AxLab-UofC/Threading-Space/general_planner_v1.0.1/images/0.png

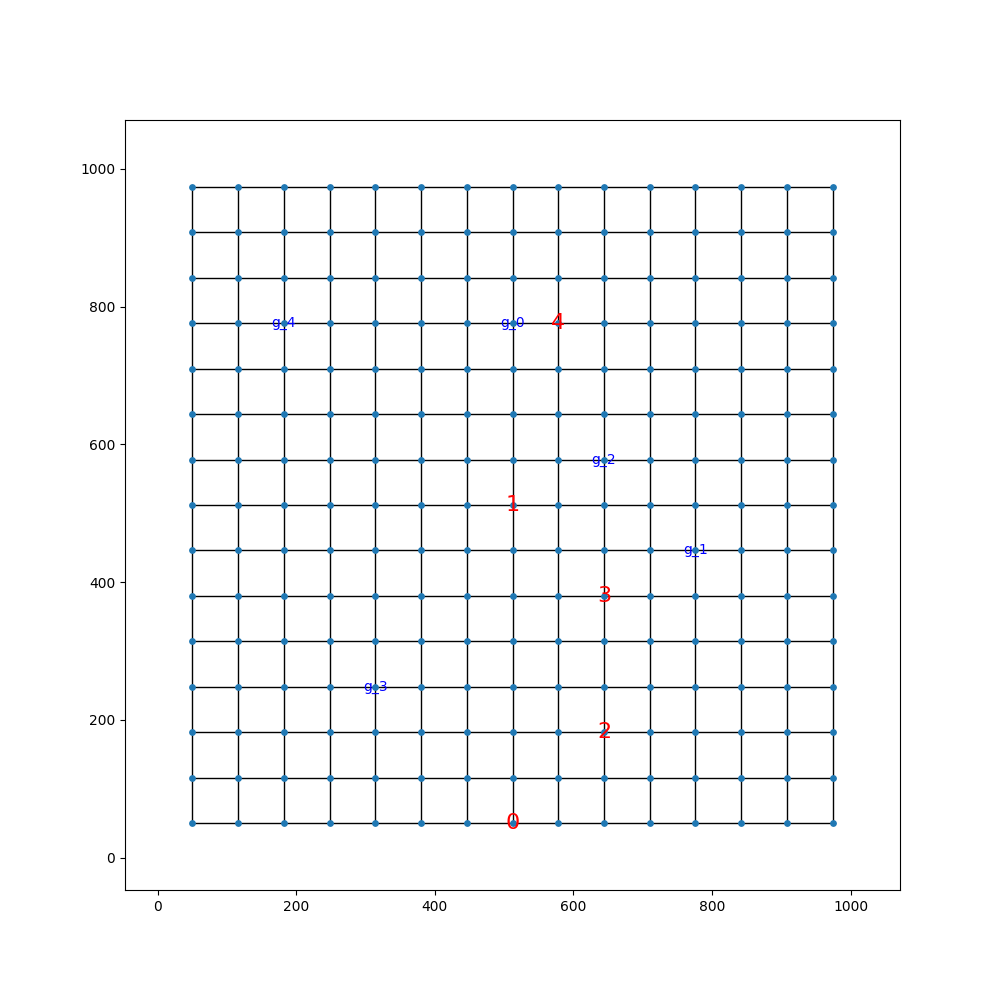
general_planner_v1.0.1/images/0.png
