AxLab-UofC/Threading-Space/Threading_Space/oscSend.pde

//basic motor control (simplified), specification found at:
//can use negative numbers to move toio backwards
//https://toio.github.io/toio-spec/en/docs/ble_motor#motor-control
void motorBasic(int cubeId, int leftspeed, int rightspeed) {
  int hostId = cubeId/cubesPerHost;
  int actualcubeid = cubeId % cubesPerHost;
  OscMessage msg = new OscMessage("/motorbasic");
  msg.add(actualcubeid);
  if (leftspeed < 0) {
    msg.add(0x01);
  } else {
    msg.add(0x02);
  }
  msg.add(leftspeed);
    if (rightspeed < 0) {
    msg.add(0x01);
  } else {
    msg.add(0x02);
  }
  msg.add(rightspeed);
  oscP5.send(msg, server[hostId]);
}

//basic motor control (advanced), specification found at:
//https://toio.github.io/toio-spec/en/docs/ble_motor#motor-control
void motorBasic(int cubeId, boolean leftforwards, int leftspeed, boolean rightforwards, int rightspeed) {
  int hostId = cubeId/cubesPerHost;
  int actualcubeid = cubeId % cubesPerHost;

  if (!cubes[actualcubeid].onFloor) {
    int tempspeed = rightspeed;
    rightspeed = leftspeed;
    leftspeed = tempspeed;

    boolean tempforwards = rightforwards;
    rightforwards = leftforwards;
    leftforwards = tempforwards;
  }

  OscMessage msg = new OscMessage("/motorbasic");
  msg.add(actualcubeid);
  if (leftforwards) {
    msg.add(0x01);
  } else {
    msg.add(0x02);
  }
  msg.add(leftspeed);
    if (rightforwards) {
    msg.add(0x01);
  } else {
    msg.add(0x02);
  }
  msg.add(rightspeed);
  oscP5.send(msg, server[hostId]);
}

//basic motor control (simplified), specification found at:
//can use negative numbers to move toio backwards
//https://toio.github.io/toio-spec/en/docs/ble_motor#motor-control
void motorDuration(int cubeId, int speed, int duration) {
  int hostId = cubeId/cubesPerHost;
  int actualcubeid = cubeId % cubesPerHost;
  OscMessage msg = new OscMessage("/motorduration");
  msg.add(actualcubeid);
  if (speed < 0) {
    msg.add(0x01);
  } else {
    msg.add(0x02);
  }
  msg.add(speed);
    if (speed < 0) {
    msg.add(0x01);
  } else {
    msg.add(0x02);
  }
  msg.add(speed);
  msg.add(duration);
  oscP5.send(msg, server[hostId]);
}

//basic motor control (simplified), specification found at:
//can use negative numbers to move toio backwards
//https://toio.github.io/toio-spec/en/docs/ble_motor#motor-control
void motorDuration(int cubeId, int leftspeed, int rightspeed, int duration) {
  int hostId = cubeId/cubesPerHost;
  int actualcubeid = cubeId % cubesPerHost;
  OscMessage msg = new OscMessage("/motorduration");
  msg.add(actualcubeid);
  if (leftspeed < 0) {
    msg.add(0x01);
  } else {
    msg.add(0x02);
  }
  msg.add(leftspeed);
    if (rightspeed < 0) {
    msg.add(0x01);
  } else {
    msg.add(0x02);
  }
  msg.add(rightspeed);
  msg.add(duration);
  
  oscP5.send(msg, server[hostId]);
}

//basic motor control (advanced), specification found at:
//https://toio.github.io/toio-spec/en/docs/ble_motor#motor-control
void motorDuration(int cubeId, boolean leftforwards, int leftspeed, boolean rightforwards, int rightspeed, int duration) {
  int hostId = cubeId/cubesPerHost;
  int actualcubeid = cubeId % cubesPerHost;
  OscMessage msg = new OscMessage("/motorduration");
  msg.add(actualcubeid);
  if (leftforwards) {
    msg.add(0x01);
  } else {
    msg.add(0x02);
  }
  msg.add(leftspeed);
    if (rightforwards) {
    msg.add(0x01);
  } else {
    msg.add(0x02);
  }
  msg.add(rightspeed);
  msg.add(duration);
  oscP5.send(msg, server[hostId]);
}

//motor control with target specified (simplified), specification found at:
//https://toio.github.io/toio-spec/en/docs/ble_motor#motor-control-with-target-specified
//control, timeout, maxspeed, and speed change are preset
void motorTarget(int cubeId, int mode, int x, int y, int theta){
  int hostId = cubeId/cubesPerHost;
  int actualcubeid = cubeId % cubesPerHost;

   if (!cubes[cubeId].onFloor) {
    x = xmax - x + xmin;;
    theta = 360 - theta;
  }

  OscMessage msg = new OscMessage("/motortarget");
  msg.add(actualcubeid);
  msg.add(mode);
  msg.add(x);
  msg.add(y);
  msg.add(theta);
  oscP5.send(msg, server[hostId]);
}

//motor control with target specified (advanced), specification found at:
//https://toio.github.io/toio-spec/en/docs/ble_motor#motor-control-with-target-specified
void motorTarget(int cubeId, int control, int timeout, int mode, int maxspeed, int speedchange,  int x, int y, int theta){
  int hostId = cubeId/cubesPerHost;
  int actualcubeid = cubeId % cubesPerHost;

  if (!cubes[cubeId].onFloor) {
    x = xmax - x + xmin;;
    theta = 360 - theta;
  }

  OscMessage msg = new OscMessage("/motortarget");
  msg.add(actualcubeid);
  msg.add(control);
  msg.add(timeout);
  msg.add(mode);
  msg.add(maxspeed);
  msg.add(speedchange);
  msg.add(x);
  msg.add(y);
  msg.add(theta);
  oscP5.send(msg, server[hostId]);
}

//motor control with multiple targets specified (simplified), specification found at:
//https://toio.github.io/toio-spec/en/docs/ble_motor#motor-control-with-target-specified
//targets should be formatted as {x, y, theta} or {x, y}. Unless specified, theta = 0
void motorMultiTarget(int cubeId, int mode, int[][] targets) {
  int hostId = cubeId/cubesPerHost;
  int actualcubeid = cubeId % cubesPerHost;
  OscMessage msg = new OscMessage("/multitargetsimple");
  msg.add(actualcubeid);
  msg.add(mode);
  for (int i = 0; i < targets.length; i++) {
    for (int j = 0; j < targets[i].length; j++) {
      if (j == 1 && !cubes[actualcubeid].onFloor) { 
        msg.add(ymax - targets[i][j]);
      } else {
        msg.add(targets[i][j]);
      }
    }
    
    if (targets[i].length == 2) {
      msg.add(0);
    }
  }
  oscP5.send(msg, server[hostId]);
}

//motor control with multiple targets specified (advanced), specification found at:
//https://toio.github.io/toio-spec/en/docs/ble_motor#motor-control-with-target-specified
//targets should be formatted as {x, y, theta} or {x, y}. Unless specified, theta = 0
void motorMultiTarget(int cubeId, int control, int timeout, int mode, int maxspeed, int speedchange,  int[][] targets){
  int hostId = cubeId/cubesPerHost;
  int actualcubeid = cubeId % cubesPerHost;
  OscMessage msg = new OscMessage("/multitarget");
  msg.add(actualcubeid);
  msg.add(control);
  msg.add(timeout);
  msg.add(mode);
  msg.add(maxspeed);
  msg.add(speedchange);
  
  for (int i = 0; i < targets.length; i++) {
    for (int j = 0; j < targets[i].length; j++) {
      if (j == 1 && !cubes[actualcubeid].onFloor) { 
        msg.add(ymax - targets[i][j]);
      } else {
        msg.add(targets[i][j]);
      }
    }
    
    if (targets[i].length == 2) {
      msg.add(0);
    }
  }
  oscP5.send(msg, server[hostId]);
}

//would need to change rotational velocity for threading space project, can be done if we need this function
//motor control with acceleration specified, specification can be found at:
//https://toio.github.io/toio-spec/en/docs/ble_motor#motor-control-with-acceleration-specified
void motorAcceleration(int cubeId, int speed, int a, int rotateVelocity, int rotateDir, int dir, int priority, int duration){
  OscMessage msg = new OscMessage("/motoracceleration");
  int hostId = cubeId/cubesPerHost;
  int actualcubeid = cubeId % cubesPerHost;
  msg.add(actualcubeid);
  msg.add(speed);
  msg.add(a);
  msg.add(rotateVelocity);
  msg.add(rotateDir);
  msg.add(dir);
  msg.add(priority);
  msg.add(duration);
  oscP5.send(msg, server[hostId]);
  oscP5.send(msg, server[hostId]);
}

//activating LED on bottom of toio, specification can be found at:
//https://toio.github.io/toio-spec/en/docs/ble_light
void led(int cubeId, int duration, int red, int green, int blue) {
  int hostId = cubeId/cubesPerHost;
  int actualcubeid = cubeId % cubesPerHost;
  OscMessage msg = new OscMessage("/led");
  msg.add(actualcubeid);
  msg.add(duration);
  msg.add(red);
  msg.add(green);
  msg.add(blue);
  oscP5.send(msg, server[hostId]);
}

//activating LED sequence on bottom of toio, specification can be found at:
//https://toio.github.io/toio-spec/en/docs/ble_light
//lights should be formatted as {duration, red, green, blue}
void led(int cubeId, int repetitions, int[][] lights) {
  int hostId = cubeId/cubesPerHost;
  int actualcubeid = cubeId % cubesPerHost;
  OscMessage msg = new OscMessage("/led");
  msg.add(actualcubeid);
  msg.add(repetitions);
  msg.add(lights.length);

  for (int i = 0; i < lights.length; i++) {
    msg.add(lights[i][0]);
    msg.add(1);
    msg.add(1);
     
    for (int j = 1; j < lights[i].length; j++) {
       msg.add(lights[i][j]);
    }
  } 
  oscP5.send(msg, server[hostId]);
}


//play sound effects, specification can be found at:
//https://toio.github.io/toio-spec/en/docs/ble_sound
void sound(int cubeId, int soundeffect, int volume) {
  int hostId = cubeId/cubesPerHost;
  int actualcubeid = cubeId % cubesPerHost;
  OscMessage msg = new OscMessage("/sound");
  msg.add(actualcubeid);
  msg.add(soundeffect);
  msg.add(volume);
  oscP5.send(msg, server[hostId]);
}

//play Midi Note (single), specification can be found at:
//https://toio.github.io/toio-spec/en/docs/ble_sound/#playing-the-midi-note-numbers
void midi(int cubeId, int duration, int noteID, int volume) {
  int hostId = cubeId/cubesPerHost;
  int actualcubeid = cubeId % cubesPerHost;
  OscMessage msg = new OscMessage("/midi");
  msg.add(actualcubeid);
  msg.add(duration);
  msg.add(noteID);
  msg.add(volume);
  oscP5.send(msg, server[hostId]);
}

//play Midi Notes (advanced), specification can be found at:
//https://toio.github.io/toio-spec/en/docs/ble_sound/#playing-the-midi-note-numbers
//targets should be formatted as {duration, noteID, volume} or {duration, noteID}. Unless specified, volume = 255
void midi(int cubeId, int repetitions, int[][] notes) {
  int hostId = cubeId/cubesPerHost;
  int actualcubeid = cubeId % cubesPerHost;
  OscMessage msg = new OscMessage("/midi");
  msg.add(actualcubeid);
  msg.add(repetitions);
  msg.add(notes.length);
  
  for (int i = 0; i < notes.length; i++) {
    for (int j = 0; j < notes[i].length; j++) {
      msg.add(notes[i][j]);
    }
    
    if (notes[i].length == 2) {
      msg.add(255);
    }
  }
  oscP5.send(msg, server[hostId]);
}

//request for motion detection information, specification can be found at:
//https://toio.github.io/toio-spec/en/docs/ble_sensor
void motionRequest(int cubeId) {
  int hostId = cubeId/cubesPerHost;
  int actualcubeid = cubeId % cubesPerHost;
  OscMessage msg = new OscMessage("/motion");
  msg.add(actualcubeid);
  oscP5.send(msg, server[hostId]);
}

//request for magnetic sensor information, specification can be found at:
//https://toio.github.io/toio-spec/en/docs/ble_magnetic_sensor
void magneticRequest(int cubeId) {
  int hostId = cubeId/cubesPerHost;
  int actualcubeid = cubeId % cubesPerHost;
  OscMessage msg = new OscMessage("/magnetic");
  msg.add(actualcubeid);
  oscP5.send(msg, server[hostId]);
}

//request for cube rotation information (in Eulers), specification can be found at:
//https://toio.github.io/toio-spec/en/docs/ble_high_precision_tilt_sensor
void postureRequest(int cubeId) {
    int hostId = cubeId/cubesPerHost;
    int actualcubeid = cubeId % cubesPerHost;
    OscMessage msg = new OscMessage("/postureeuler");
    msg.add(actualcubeid);
    oscP5.send(msg, server[hostId]);
}

//request for cube rotation information, specification can be found at:
//https://toio.github.io/toio-spec/en/docs/ble_high_precision_tilt_sensor
void postureRequest(int cubeId, boolean euler) {
    int hostId = cubeId/cubesPerHost;
    int actualcubeid = cubeId % cubesPerHost;
    OscMessage msg;
    if (euler) {
      msg = new OscMessage("/postureeuler");
    } else {
      msg = new OscMessage("/posturequaternion");
    }
     msg.add(actualcubeid);
     oscP5.send(msg, server[hostId]);
}
