AxLab-UofC/Threading-Space/Threading_Space/display.pde

//For Threading Space Style
color StringCol = color(0, 255, 255);
color backgroundCol = (180);
color ceilingCol = color(255, 255, 255);
color floorCol = color(255, 255, 255);
int stringWeight = 4;

int toioCylinderR = 12;
int toioCylinderH = 10;


color toioStrokeCol = 200;
color toioFillCol = color (255, 255, 255, 200);

color[] toioTrackedStrokeCol = {color (0, 0, 255, 200), color (255, 0, 0, 200)};
color toioTrackedFillCol = color (255, 255, 255, 50);


void drawDisplay() {
  if (guiState == GUImode.SELECT) {
    StringCol = color(0, 255, 255, 75);
  }
  
  background (backgroundCol);
  noStroke();
  fill(200);
  rectMode(CENTER);
  background(255);


  long now = System.currentTimeMillis();

  //draw the "mats"
  background (backgroundCol);
  noStroke();
  fill(200);
  rectMode(CENTER);

  //draw floor
  pushMatrix();
  fill(floorCol);
  translate(0, 0, -vert);
  rect(0, 0, xmax, ymax);
  popMatrix();

  //draw ceiling
  pushMatrix();
  fill(ceilingCol);
  translate(0, 0, vert);
  rect(0, 0, xmax, ymax);
  popMatrix();
  
  //For debugging the offset
  //stroke(255, 0, 0); // Red line
  //strokeWeight(2);
  //line(-xmax/2, -ymax/2, vert, xmax/2, ymax/2, vert); 
  
  //stroke(0, 0, 255); // Blue line
  //line(-xmax/2, -ymax/2, -vert, xmax/2, ymax/2, -vert);


  for (int i = 0; i < nPairs; i++) {
    pairs[i].checkActive(now);
    boolean topActive = pairs[i].t.isActive;
    boolean bottomActive = pairs[i].b.isActive;

    pushMatrix();
    translate(-xmax/2, -ymax/2, 0);
    stroke(200);
    fill(255);
    strokeWeight(1);

    //Draw Top Toio
    pushMatrix();
    if (visualOn) {
      pushMatrix();
      translate(pairsViz[i].t.x, pairsViz[i].t.y, vert - 5);

      drawVelocityLine(pairsViz[i].t.vx, pairsViz[i].t.vy);



      rotate(pairsViz[i].t.theta * PI/180);
      //box(12, 12, 7);
      drawCylinder(10, toioCylinderR, toioCylinderH, toioStrokeCol, toioFillCol);
      popMatrix();



      if (debugMode) {
        if (topActive) {
          if (cubes[i].isActive) {
            stroke(1);
            line(pairsViz[i].t.x, pairsViz[i].t.y, vert - 5, xmax - pairs[i].t.x, pairs[i].t.y, vert - 5); //line between target and actual toio pos
          }

          pushMatrix();
          translate(xmax - pairs[i].t.x, pairs[i].t.y, vert - 5);
          
          pushMatrix();
          translate(0, 10, -5);
          rotateX(-PI/2);

          fill(toioTrackedStrokeCol[pairs[i].t.id/cubesPerHost]);
          textSize(30);
          text(pairs[i].t.id + ": " + pairs[i].t.battery + "%", -2 * toioCylinderR, 2 * toioCylinderH, 0);
          popMatrix();
          


          rotate(pairs[i].t.theta * PI/180);
          //box(12, 12, 7);
          drawCylinder(10, toioCylinderR, toioCylinderH, toioTrackedStrokeCol[pairs[i].t.id/cubesPerHost], toioTrackedFillCol);
          popMatrix();
        }
      }
    } else {
      if (topActive) {
        translate(xmax - pairs[i].t.x, pairs[i].t.y, vert - 5);

        rotate(pairs[i].t.theta * PI/180);
        //box(12, 12, 7);
        drawCylinder(10, toioCylinderR, toioCylinderH, toioStrokeCol, toioFillCol);
      }
    }
    popMatrix();



    //Draw Bottom Toio
    pushMatrix();
    if (visualOn) { // enable Visualization of Animation
      pushMatrix();
      translate(pairsViz[i].b.x, pairsViz[i].b.y, -vert + 5);

      drawVelocityLine(pairsViz[i].b.vx, pairsViz[i].b.vy);

      rotate(pairsViz[i].b.theta * PI/180);
      //box(12, 12, 7);
      drawCylinder(10, toioCylinderR, toioCylinderH, toioStrokeCol, toioFillCol);

      popMatrix();

      if (debugMode) { // overlay current toio positions, velocity, and taregetting line
        if (cubes[i].isActive) {
          stroke(1);
          line(pairsViz[i].b.x, pairsViz[i].b.y, -vert + 5, pairs[i].b.x, pairs[i].b.y, -vert + 5);
        }

        if (bottomActive) {
          pushMatrix();
          translate(pairs[i].b.x, pairs[i].b.y, -vert + 5);

          pushMatrix();
          translate(0, 10, 20);
          rotateX(-PI/2);

          fill(toioTrackedStrokeCol[pairs[i].b.id/cubesPerHost]);
          textSize(30);
          text(pairs[i].b.id + ": " + pairs[i].b.battery + "%", -2 * toioCylinderR, -2 * toioCylinderH, 0);

          popMatrix();
          
          rotate(pairs[i].b.theta * PI/180);

          drawCylinder(10, toioCylinderR, toioCylinderH, toioTrackedStrokeCol[pairs[i].b.id/cubesPerHost], toioTrackedFillCol);
          popMatrix();
        }
      }
    } else {
      if (bottomActive) {
        translate(pairs[i].b.x, pairs[i].b.y, -vert + 5);

        drawVelocityLine(pairsViz[i].b.vx, pairsViz[i].b.vy);

        rotate(pairs[i].b.theta * PI/180);
        //box(12, 12, 7);
        drawCylinder(10, toioCylinderR, toioCylinderH, toioStrokeCol, toioFillCol);
      }
    }
    popMatrix();


    //Draw strings
    stroke(StringCol);
    strokeWeight(stringWeight);
    if (visualOn) {
      if (debugMode) {
        stroke(color(191+(64*sin(i)), 191+(64*sin(i + (PI/4))), 191+(64*sin(i + (PI/2)))));
      }
      line(pairsViz[i].t.x, pairsViz[i].t.y, vert - toioCylinderH/2, pairsViz[i].b.x, pairsViz[i].b.y, -vert + toioCylinderH/2);
    } else {
      if (topActive && bottomActive) {
        if (debugMode) {
          stroke(color(191+sin(i), 191+sin(i + (PI/4)), 191+sin(i + (PI/4))));
        }
        line(xmax - pairs[i].t.x, pairs[i].t.y, vert - toioCylinderH/2, pairs[i].b.x, pairs[i].b.y, -vert+ toioCylinderH/2);
      }
    } 

    popMatrix();
  }
  
  
  for (int i = nPairs * 2; i < nCubes; i++) {
    pushMatrix();
    translate(cubes[i].x -xmax/2, cubes[i].y -ymax/2, -vert + 5);
    drawCylinder(10, toioCylinderR, toioCylinderH, toioStrokeCol, toioFillCol);
    popMatrix();
  } 
  
}

//Function to draw Cylinder
void drawCylinder( int sides, float r, float h, color strokeColor, color fillColor)
{

  float angle = 360 / sides;
  float halfHeight = h / 2;
  strokeWeight(2);
  stroke(strokeColor);
  fill(fillColor);
  // draw top of the tube
  beginShape();
  for (int i = 0; i < sides; i++) {
    float x = cos( radians( i * angle ) ) * r;
    float y = sin( radians( i * angle ) ) * r;
    vertex( x, y, -halfHeight);
  }
  endShape(CLOSE);

  // draw bottom of the tube
  beginShape();
  for (int i = 0; i < sides; i++) {
    float x = cos( radians( i * angle ) ) * r;
    float y = sin( radians( i * angle ) ) * r;
    vertex( x, y, halfHeight);
  }
  endShape(CLOSE);

  // draw sides
  beginShape(TRIANGLE_STRIP);
  noStroke();
  for (int i = 0; i < sides + 1; i++) {
    float x = cos( radians( i * angle ) ) * r;
    float y = sin( radians( i * angle ) ) * r;
    vertex( x, y, halfHeight);
    vertex( x, y, -halfHeight);
  }
  endShape(CLOSE);

  strokeWeight(2);
  stroke(255, 0, 0);
  // Red line to represent robot's theta
  line(0, 0, halfHeight, r, 0, halfHeight);
  line(0, 0, -halfHeight, r, 0, -halfHeight);
}


//

void drawVelocityLine(float vx, float vy) {

  if (debugMode) {
    float angle = atan2(vy, vx) + PI ;
    float scale = 1000; // scale the lenght of arrow

    float x_begin = cos(angle) * toioCylinderR;
    float y_begin = sin(angle) * toioCylinderR;

    stroke(0, 255, 0);
    strokeWeight(5);
    line(x_begin, y_begin, x_begin - vx*scale, y_begin - vy*scale);
  }
}
