AxLab-UofC/Threading-Space/Threading_Space/anim_interactive.pde

int buffer = 50;

int newymax = ymax - buffer;
int newymin = ymin + buffer;

float prevs = 0;
boolean flip = false;

boolean sign(float num) {
  return (num > 0);
}

int[][] lineGen() {
  int xmid = (cubes[10].x + cubes[11].x) / 2;
  int ymid = (cubes[10].y + cubes[11].y) / 2;
  float frequency = 2; 
  float time = millis() / 1000.0;
  //cubes[10].motor(true, 10, false, 50);
  
  
  
  int[][] targets = new int[nPairs][3];
  
  if (cubes[10].y - cubes[11].y != 0) {
    float s = (float) (cubes[10].x - cubes[11].x) / (float) (cubes[10].y - cubes[11].y);
    int[] limits = lineLimits(ymid, xmid, s);
    
    if (sign(s) != sign(prevs) && abs(prevs) > 1) {
      println("Flip!");
      flip = !flip;
    }
    
    for (int i = 0; i < nPairs; i++) {
      int circx;
      if (flip) {
        circx = (int) lerp(limits[0], limits[1], 1 - (float) i / (nPairs - 1));
      } else {
        circx = (int) lerp(limits[0], limits[1], (float) i / (nPairs - 1));
      }
      targets[i][0] = int(circx + 15 * cos(frequency * time + (i * PI / nPairs)));
      targets[i][1] = lineGet(ymid, xmid, s, circx);
      targets[i][2] = 0;     
    }
    prevs = s;
  } else {
      int[] limits = lineLimits(ymid, xmid, prevs);
      for (int i = 0; i < nPairs; i++) {
        int circx;
        if (flip) {
          circx = (int) lerp(limits[0], limits[1], 1 - (float) i / (nPairs - 1));
        } else {
          circx = (int) lerp(limits[0], limits[1], (float) i / (nPairs - 1));
        }
        targets[i][0] = int(circx + 15 * cos(frequency * time + (i * PI / nPairs)));
        targets[i][1] = lineGet(ymid, xmid, prevs, circx);
        targets[i][2] = 0;     
      }
  }
  
  return targets;
}

int[] lineLimits(int ymid, int xmid, float s) {
  int lefty = ymid - int(s * (xmin - xmid));
  int righty = ymid - int(s * (xmax - xmid));
  
  int leftx;
  if (lefty > newymax) {
    leftx = int(xmid + ((ymid - newymax) / s));
  } else if (lefty < newymin) {
    leftx = int(xmid + ((ymid - newymin) / s));
  } else {
    leftx = xmin + buffer;
  }
  
  int rightx;
  if (righty > newymax) {
    rightx = int(xmid + ((ymid - newymax) / s));
  } else if (righty < newymin) {
    rightx = int(xmid + ((ymid - newymin) / s));
  } else {
    rightx = xmax - buffer;
  }
  
  //int[] ret = {min(leftx, rightx), max(leftx, rightx)};
  int[] ret = {leftx, rightx};
  return ret;
}

int lineGet(int ymid, int xmid, float s, int x) {
  return ymid - int(s * (x - xmid));
}
